aqmoreira/Central-IOT/software/SimulaVLT/cruzamento.png

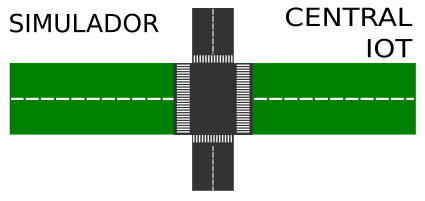
software/SimulaVLT/cruzamento.png
