aqmoreira/Central-IOT/hardware/imagens/pcb-fabricada-jlpcb.jpg

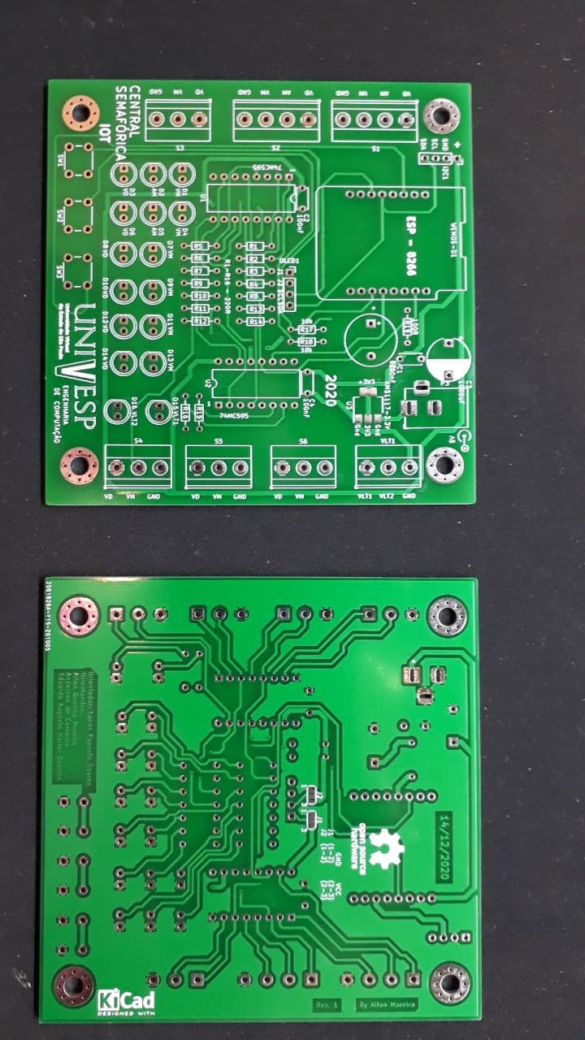
hardware/imagens/pcb-fabricada-jlpcb.jpg
