aqmoreira/Central-IOT/software/IOTCentral/imagens.h

#define UNIVESP_Logo_width 80
#define UNIVESP_Logo_height 34
const uint8_t UNIVESP_Logo_bits[] PROGMEM = {
  0x07, 0xde, 0x03, 0xfe, 0x7b, 0x3f, 0xf7, 0x07, 0x3f, 0x7f, 0x07, 0x9c,
   0x03, 0xce, 0x79, 0xbf, 0x67, 0x84, 0x3b, 0xe7, 0x06, 0x9c, 0x07, 0xcc,
   0x79, 0xbf, 0x67, 0x80, 0x31, 0xc6, 0x06, 0x8c, 0x0f, 0xcc, 0x71, 0xbf,
   0x67, 0xc0, 0x00, 0xc6, 0x06, 0x8c, 0x1f, 0xcc, 0x71, 0xbe, 0x67, 0xc0,
   0x01, 0xc6, 0x06, 0x8c, 0x1d, 0xcc, 0xf1, 0xbe, 0x63, 0xc0, 0x01, 0xc6,
   0x06, 0x8c, 0x39, 0xcc, 0xf1, 0xbe, 0x63, 0x84, 0x03, 0xc6, 0x06, 0x8c,
   0x79, 0xcc, 0xf1, 0xbe, 0xe3, 0x87, 0x07, 0xe6, 0x06, 0x8c, 0x71, 0xcc,
   0xf1, 0x9e, 0xe3, 0x07, 0x0f, 0x7e, 0x06, 0x8c, 0xe1, 0xcc, 0xe1, 0xde,
   0x63, 0x04, 0x1e, 0x06, 0x06, 0x8c, 0xe1, 0xcd, 0xe1, 0xde, 0x63, 0x00,
   0x3c, 0x06, 0x06, 0x8c, 0xc1, 0xcf, 0xe1, 0xde, 0x63, 0x00, 0x38, 0x06,
   0x06, 0x8c, 0x81, 0xcf, 0xe1, 0xdc, 0x61, 0x00, 0x30, 0x06, 0x06, 0x8c,
   0x01, 0xcf, 0xe1, 0xdd, 0x61, 0x00, 0x30, 0x06, 0x0e, 0x8c, 0x01, 0xcf,
   0xe1, 0xdd, 0x61, 0xd0, 0x30, 0x06, 0x1e, 0x8f, 0x01, 0xce, 0xe1, 0xdd,
   0x61, 0xd8, 0x38, 0x06, 0xfc, 0xdf, 0x03, 0xcc, 0xc3, 0xdd, 0xf1, 0xdf,
   0x1f, 0x0f, 0xf0, 0xde, 0x03, 0xc4, 0xc3, 0xed, 0xf1, 0x8f, 0x0f, 0x0f,
   0x00, 0x00, 0x00, 0x00, 0xc0, 0xed, 0x01, 0x00, 0x00, 0x00, 0x00, 0x00,
   0x00, 0x00, 0xc0, 0xed, 0x00, 0x00, 0x00, 0x00, 0x00, 0x00, 0x00, 0x00,
   0xc0, 0xed, 0x00, 0x00, 0x00, 0x00, 0x00, 0x00, 0x00, 0x00, 0xc0, 0xed,
   0x00, 0x00, 0x00, 0x00, 0x00, 0x00, 0x00, 0x00, 0xc0, 0xed, 0x00, 0x00,
   0x00, 0x00, 0x00, 0x00, 0x00, 0x00, 0x80, 0xe1, 0x00, 0x00, 0x00, 0x00,
   0x00, 0x00, 0x00, 0x00, 0x80, 0xe1, 0x00, 0x00, 0x00, 0x00, 0x00, 0x00,
   0x00, 0x00, 0x80, 0xf3, 0x00, 0x00, 0x00, 0x00, 0x00, 0x00, 0x00, 0x00,
   0x80, 0x73, 0x00, 0x00, 0x00, 0x00, 0x00, 0x00, 0x00, 0x00, 0x80, 0x73,
   0x00, 0x00, 0x00, 0x00, 0x00, 0x00, 0x00, 0x00, 0x80, 0x7f, 0x00, 0x00,
   0x00, 0x00, 0x00, 0x00, 0x00, 0x00, 0x80, 0x7f, 0x00, 0x00, 0x00, 0x00,
   0x00, 0x00, 0x00, 0x00, 0x00, 0x7f, 0x00, 0x00, 0x00, 0x00, 0x00, 0x00,
   0x00, 0x00, 0x00, 0x7f, 0x00, 0x00, 0x00, 0x00, 0x00, 0x00, 0x00, 0x00,
   0x00, 0x7f, 0x00, 0x00, 0x00, 0x00, 0x00, 0x00, 0x00, 0x00, 0x00, 0x3f,
   0x00, 0x00, 0x00, 0x00
  };
